hpax/SV04-Suicide-Switch-Remix/bracket/bracket.jpg

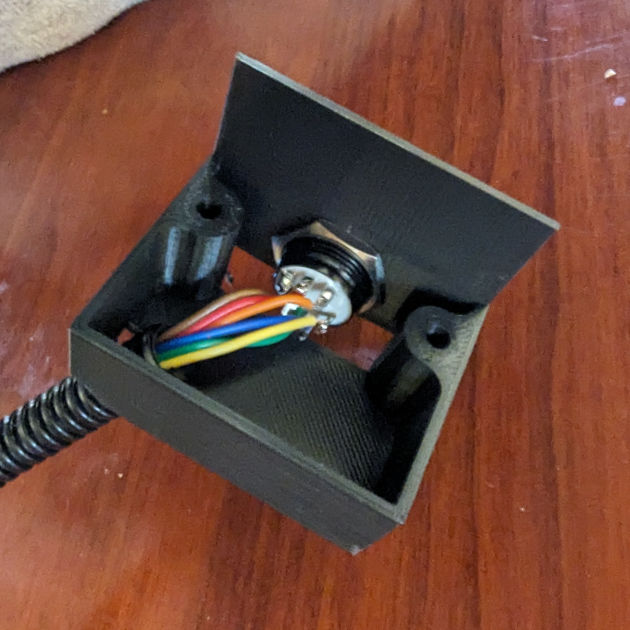
bracket/bracket.jpg
