hpax/SV04-Suicide-Switch-Remix/bracket/mounted.jpg

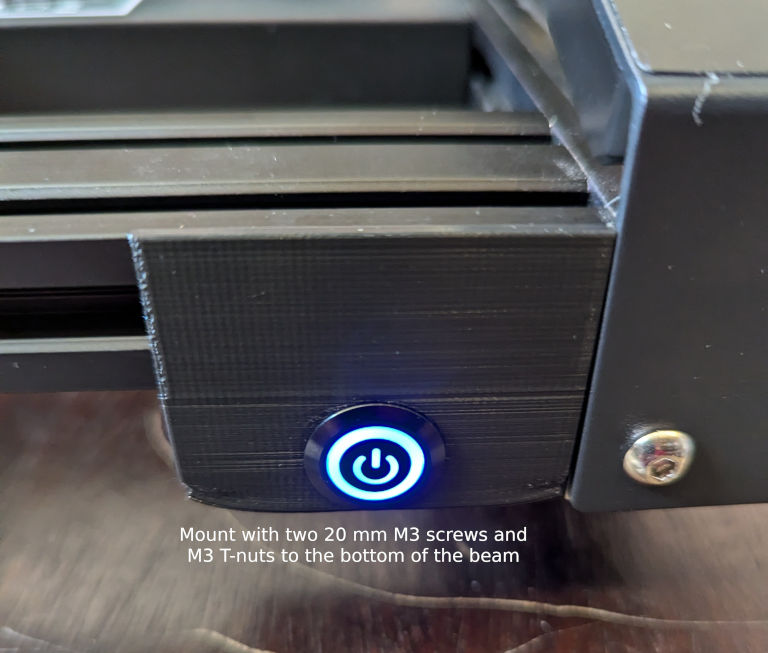
bracket/mounted.jpg
