hpax/SV04-Suicide-Switch-Remix/hw/stripboard/mounting-detail.jpg

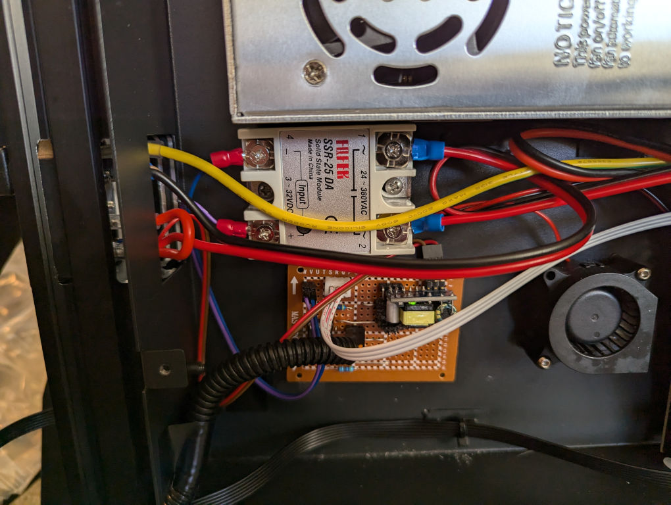
hw/stripboard/mounting-detail.jpg
