hpax/SV04-Suicide-Switch-Remix/hw/stripboard/mounting.jpg

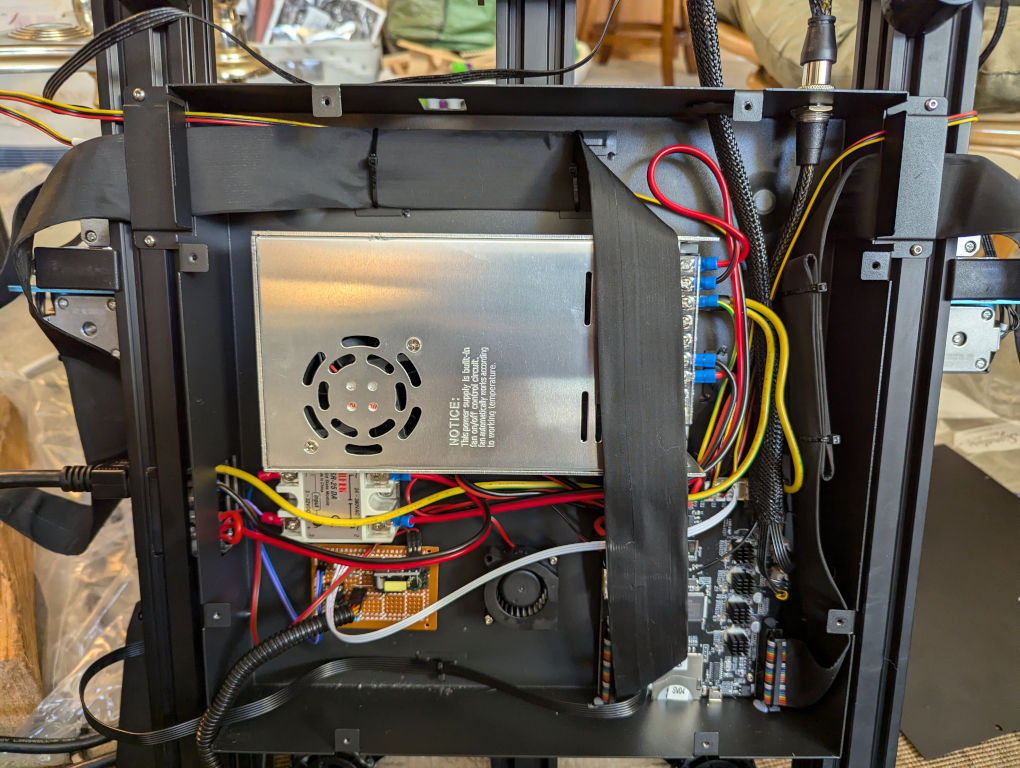
hw/stripboard/mounting.jpg
