hpax/SV04-Suicide-Switch-Remix/nightlight.h

#include <stddef.h>
#include <stdbool.h>
#include <inttypes.h>
#include <avr/eeprom.h>
#include <avr/io.h>
#include <avr/interrupt.h>
#include <avr/pgmspace.h>
#include <avr/sleep.h>
#include <util/delay.h>

#define likely(x)   __builtin_expect(!!(x), true)
#define unlikely(x) __builtin_expect(!!(x), false)
